baljo/santa_detector/images/HQ/IMG_4454.jpg

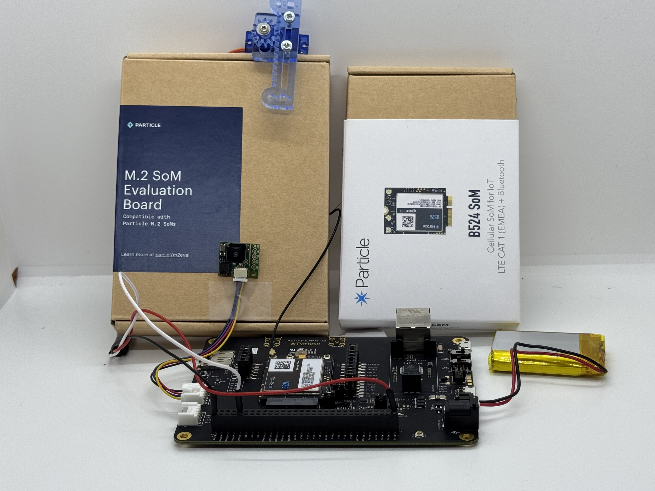
images/HQ/IMG_4454.jpg
