baljo/santa_detector/images/HQ/IMG_4455.jpg

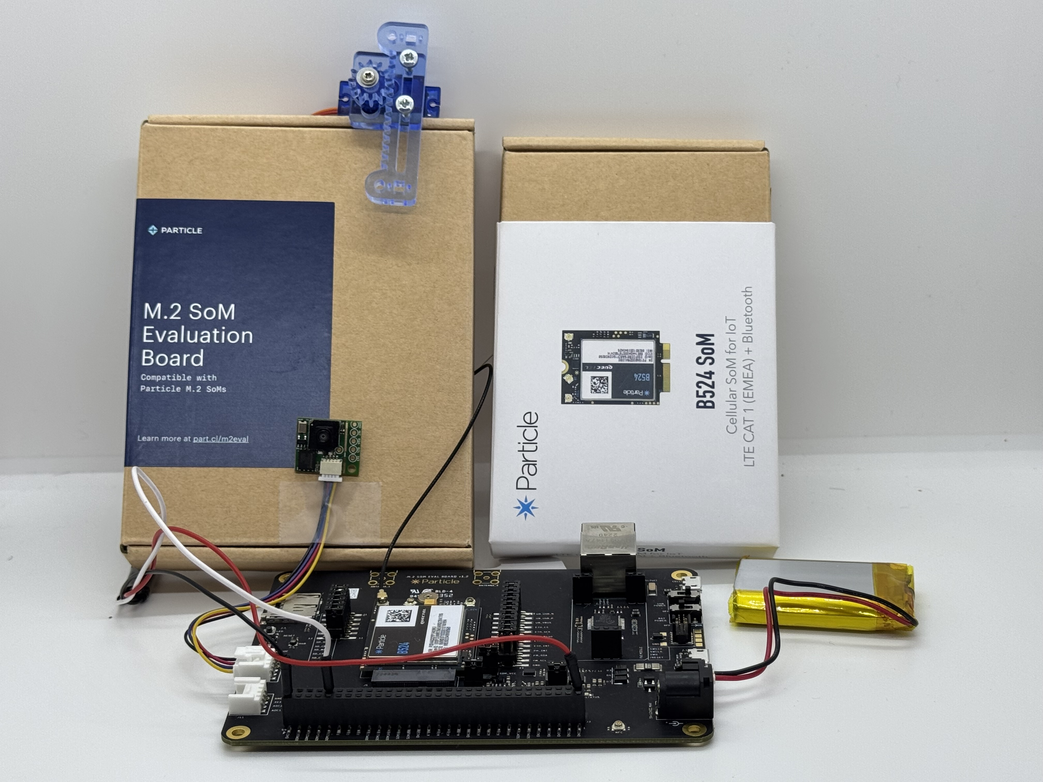
images/HQ/IMG_4455.jpg
