baljo/santa_detector/images/HQ/IMG_4456.jpg

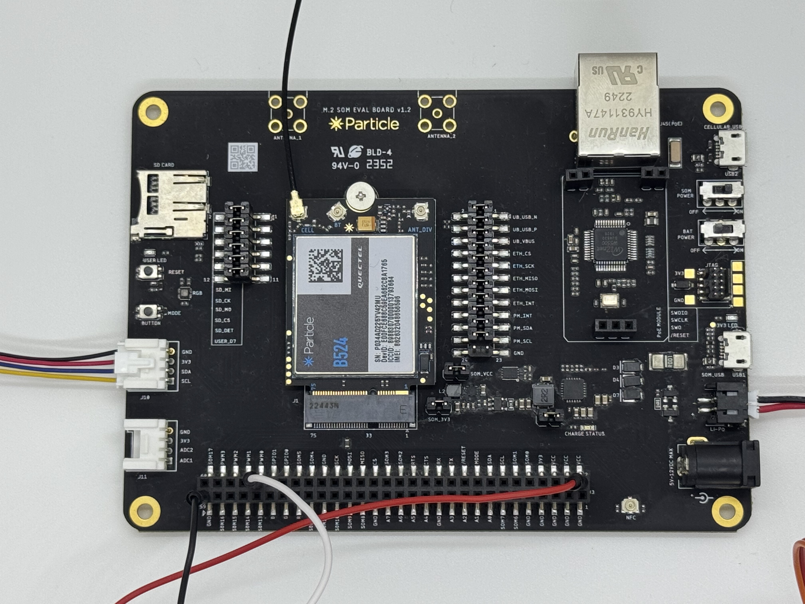
images/HQ/IMG_4456.jpg
