baljo/santa_detector/images/HQ/IMG_4458.jpg

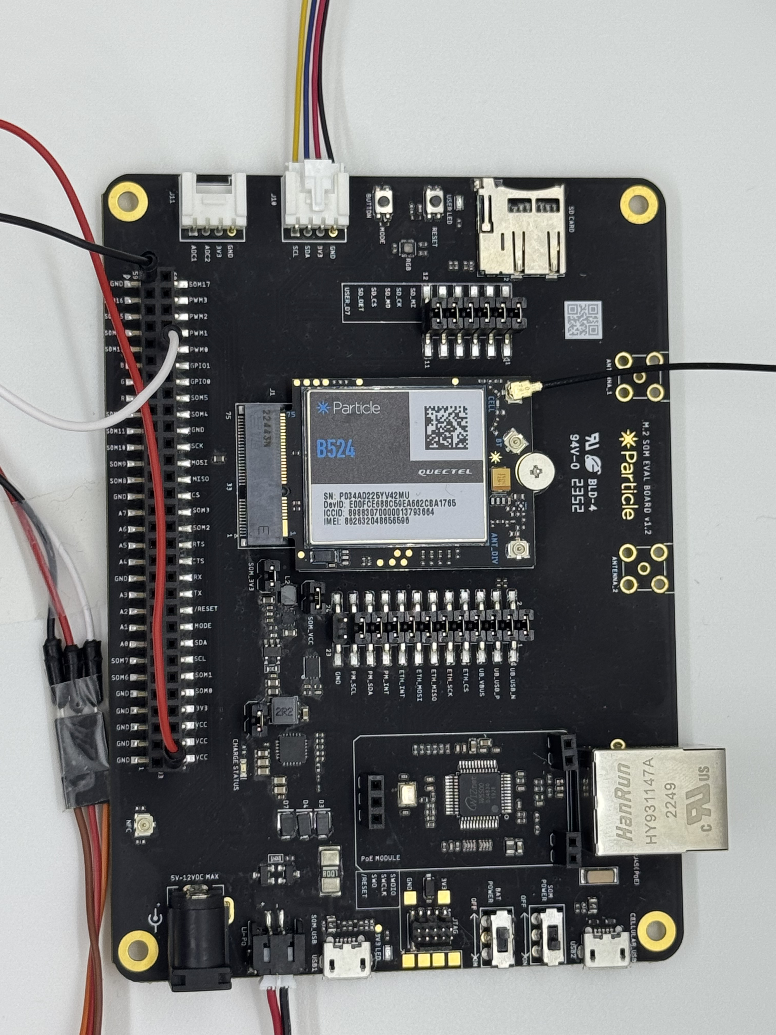
images/HQ/IMG_4458.jpg
