baljo/santa_detector/images/HQ/IMG_4462.jpg

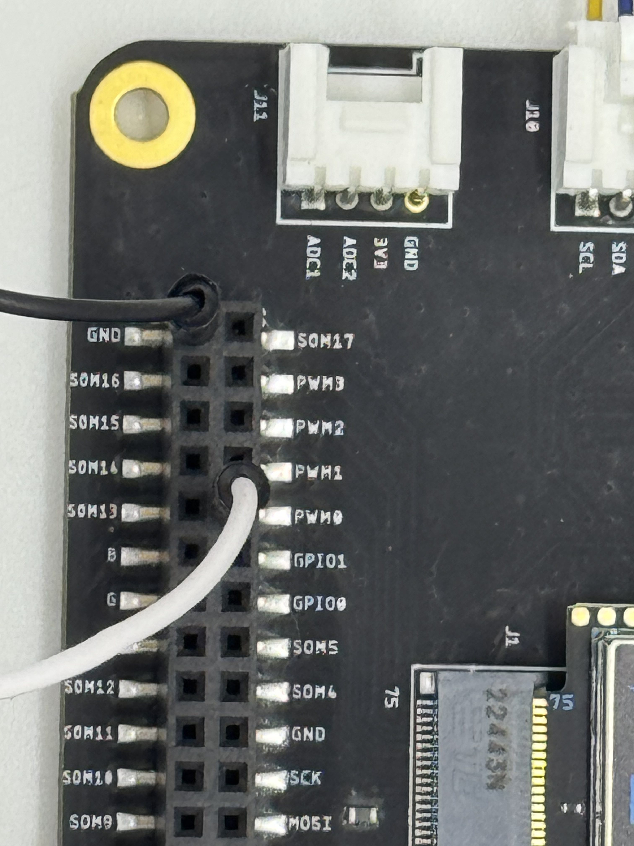
images/HQ/IMG_4462.jpg
