baljo/santa_detector/images/HQ/IMG_4465.jpg

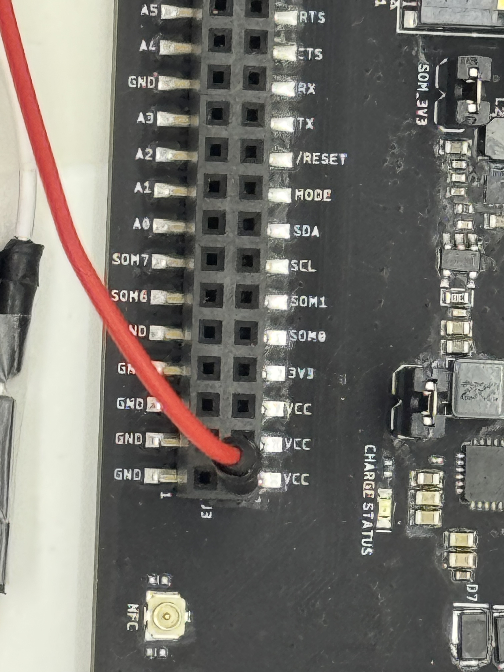
images/HQ/IMG_4465.jpg
