baljo/santa_detector/images/HQ/IMG_4468.jpg

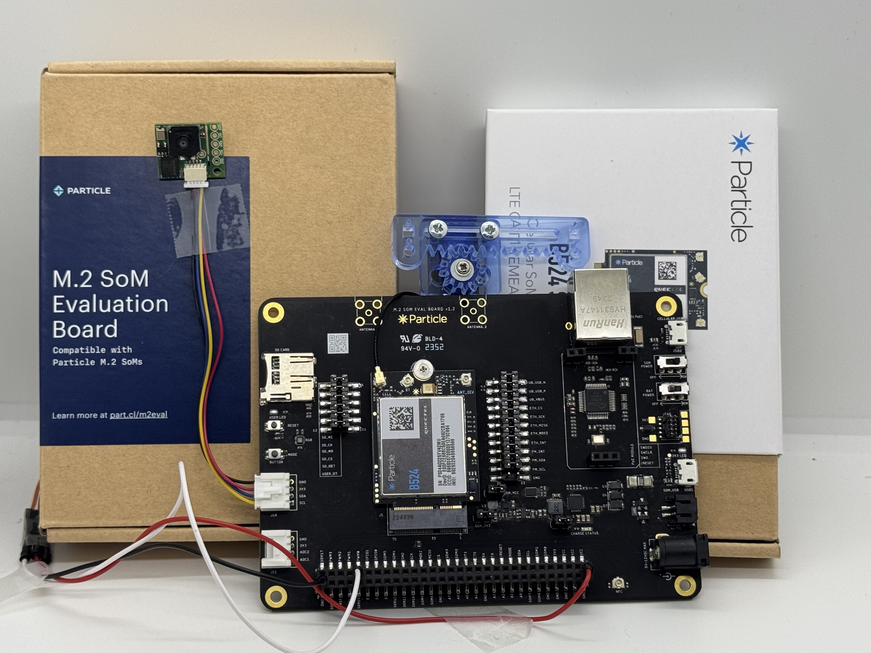
images/HQ/IMG_4468.jpg
