baljo/santa_detector/images/IMG_4441.jpg

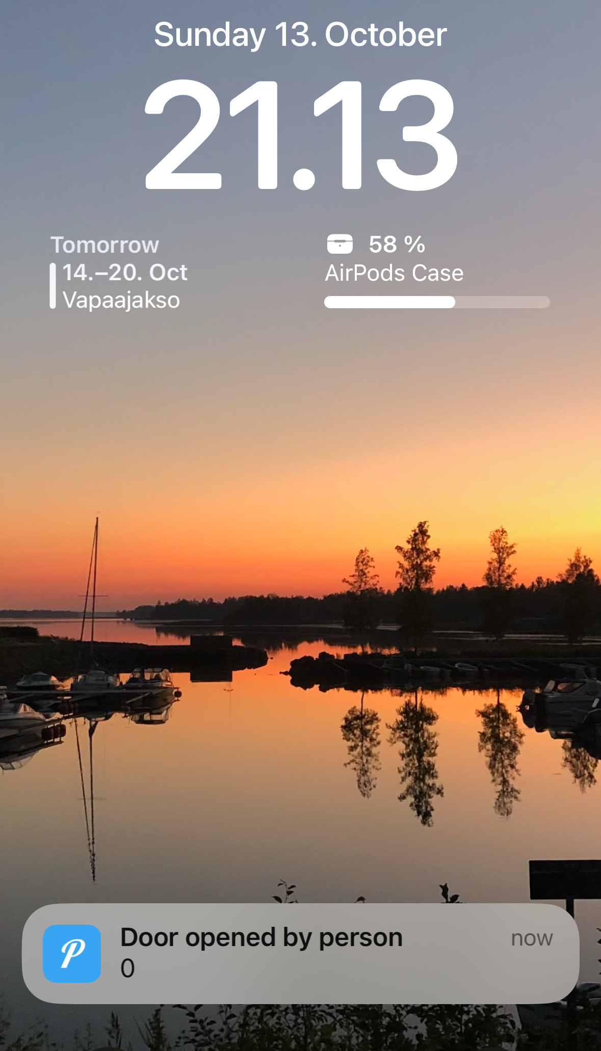
images/IMG_4441.jpg
