baljo/santa_detector/images/IMG_4443.jpg

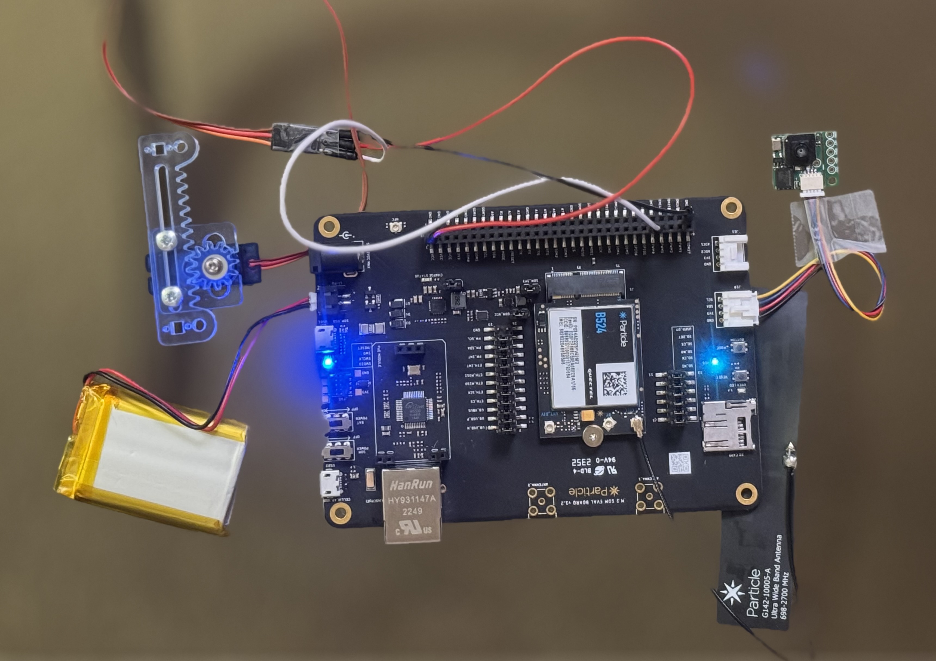
images/IMG_4443.jpg
