baljo/santa_detector/images/IMG_4446.jpg

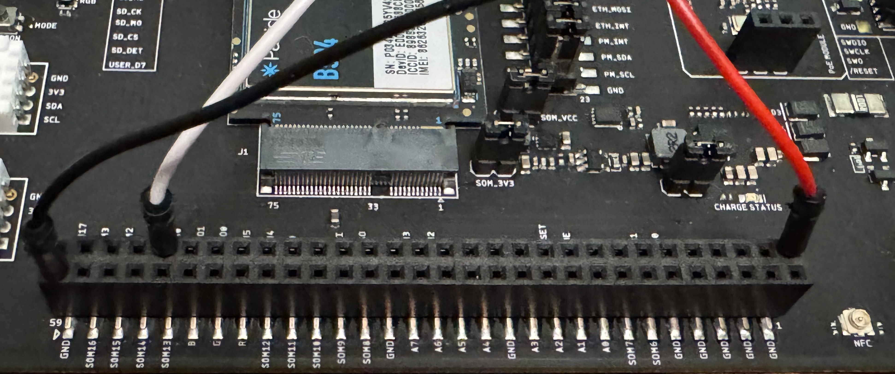
images/IMG_4446.jpg
