baljo/santa_detector/images/IMG_4451.jpg

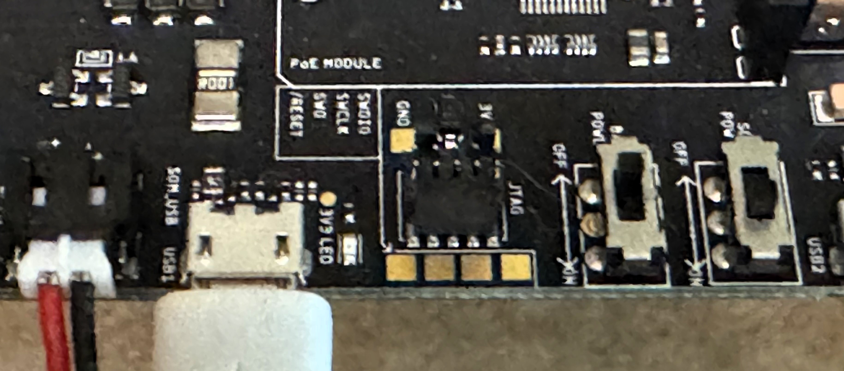
images/IMG_4451.jpg
