baljo/santa_detector/images/IMG_4453.jpg

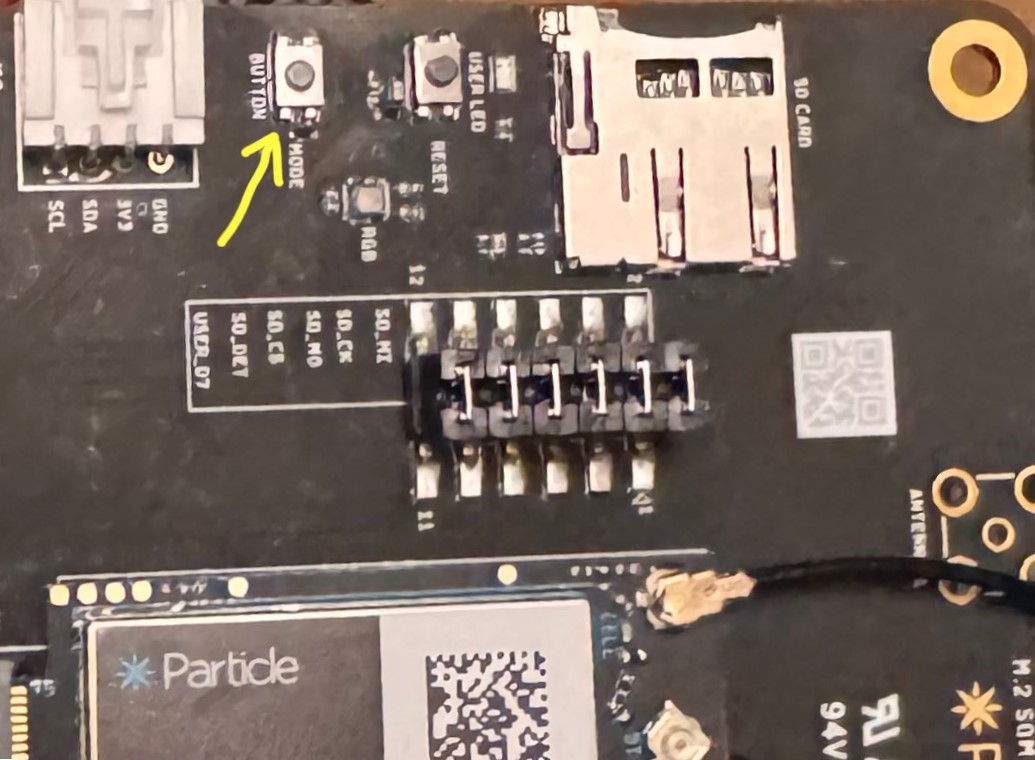
images/IMG_4453.jpg
