baljo/santa_detector/images/IMG_4468_cropped.jpg

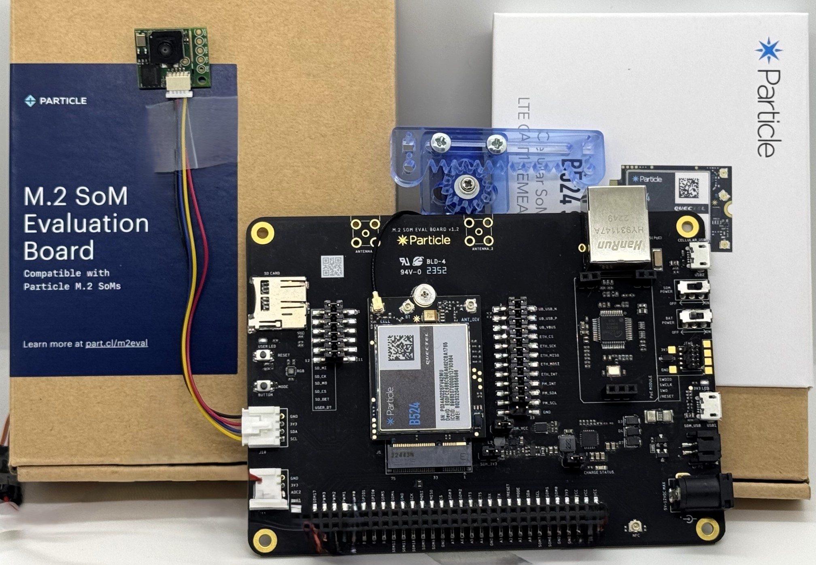
images/IMG_4468_cropped.jpg
