baljo/santa_detector/images/Overview.jpg

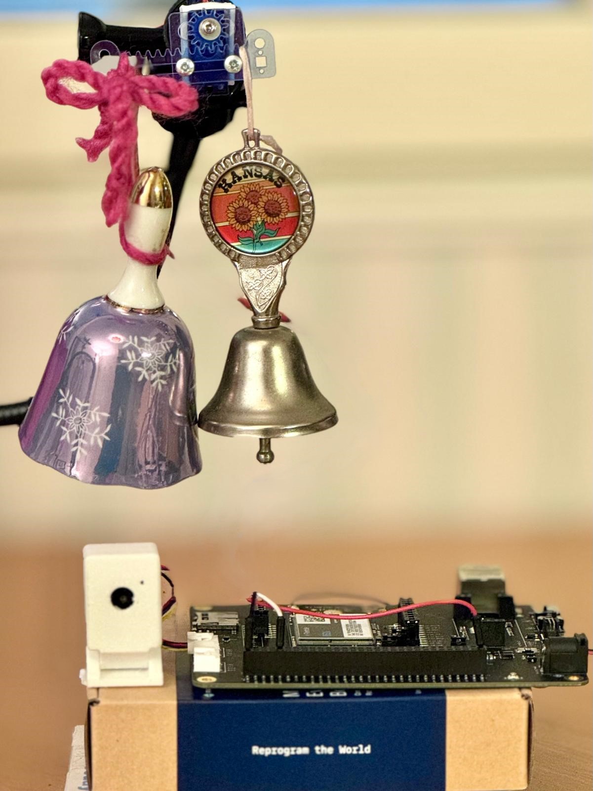
images/Overview.jpg
