baljo/santa_detector/images/Qwiic_Grove_cable.jpg

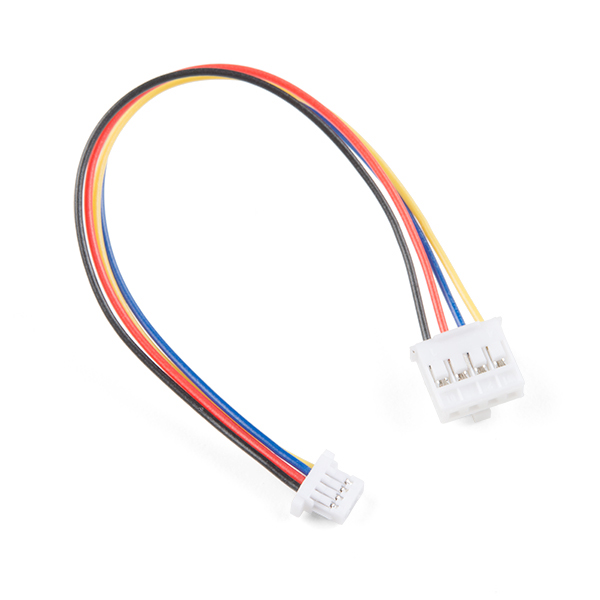
images/Qwiic_Grove_cable.jpg
