baljo/santa_detector/images/Santa_detected.png

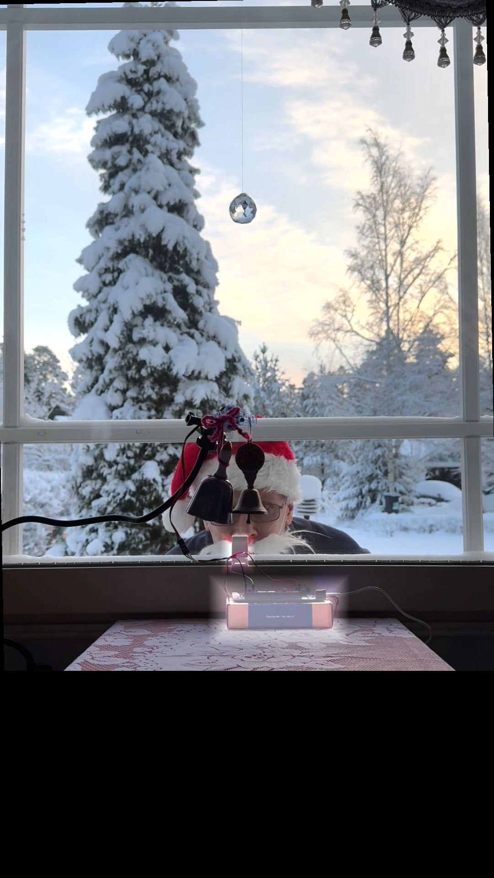
images/Santa_detected.png
