baljo/santa_detector/images/Santa_detected_2.png

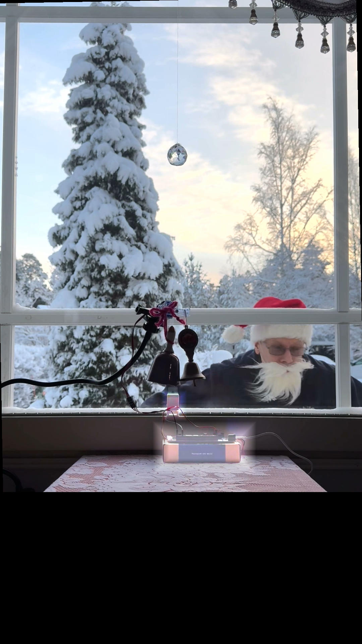
images/Santa_detected_2.png
