baljo/santa_detector/images/Shotcut_00_00_13_001.png

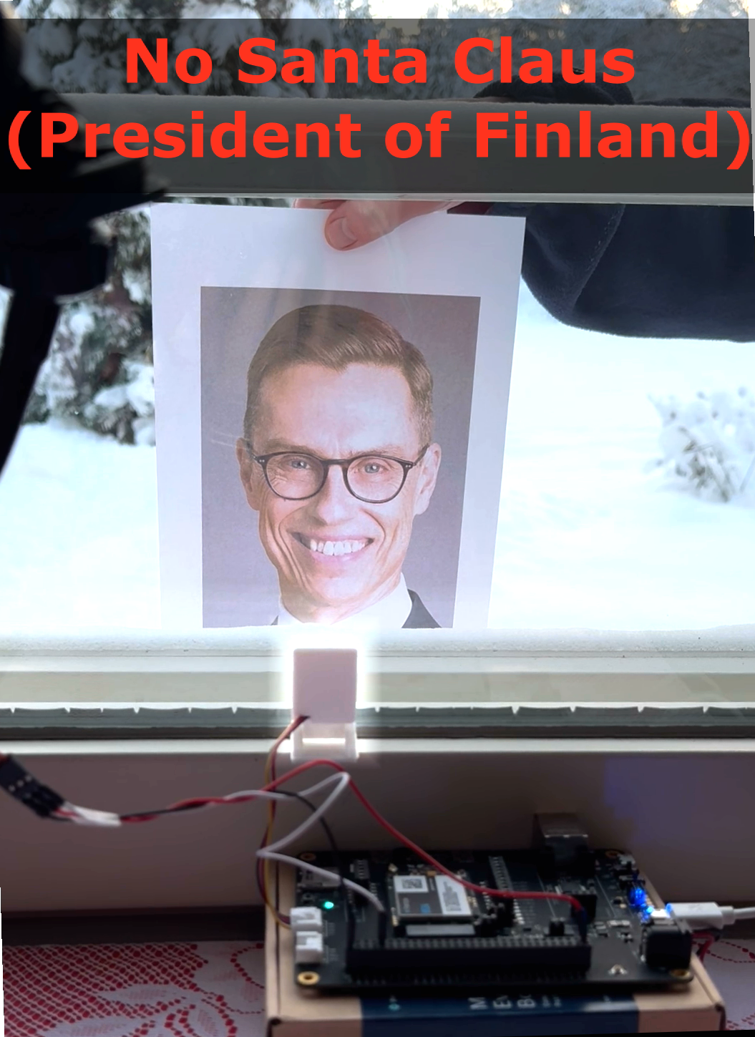
images/Shotcut_00_00_13_001.png
