baljo/santa_detector/images/Shotcut_00_00_41_537.png

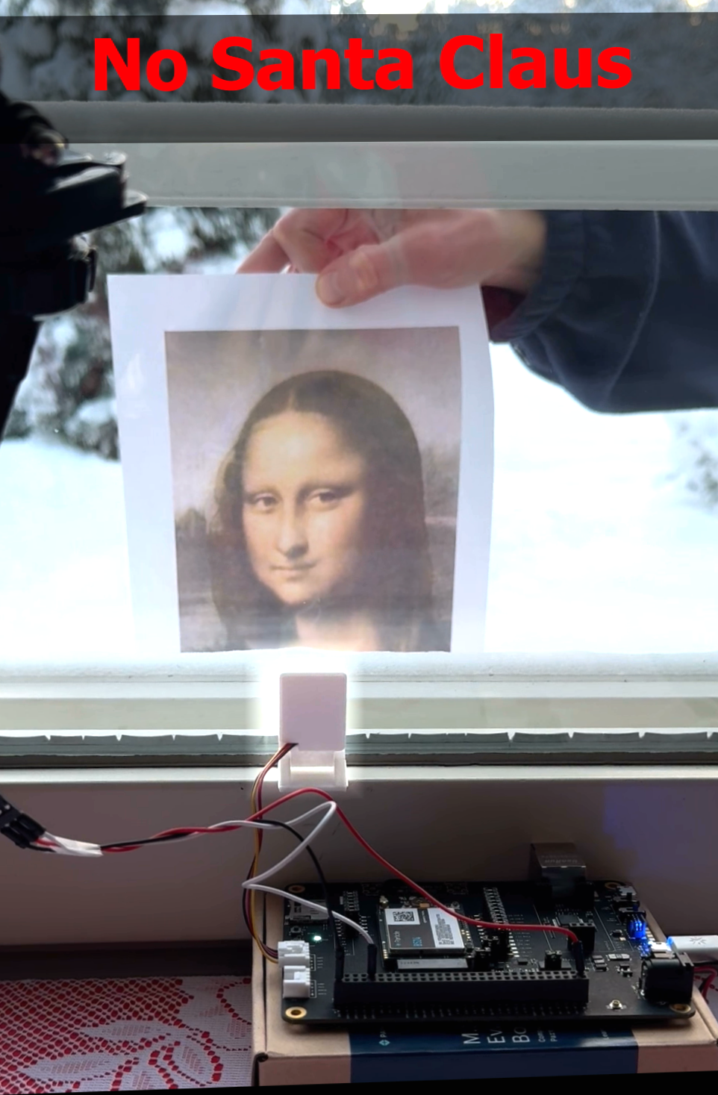
images/Shotcut_00_00_41_537.png
