baljo/santa_detector/video/Jingle Bells.jpg

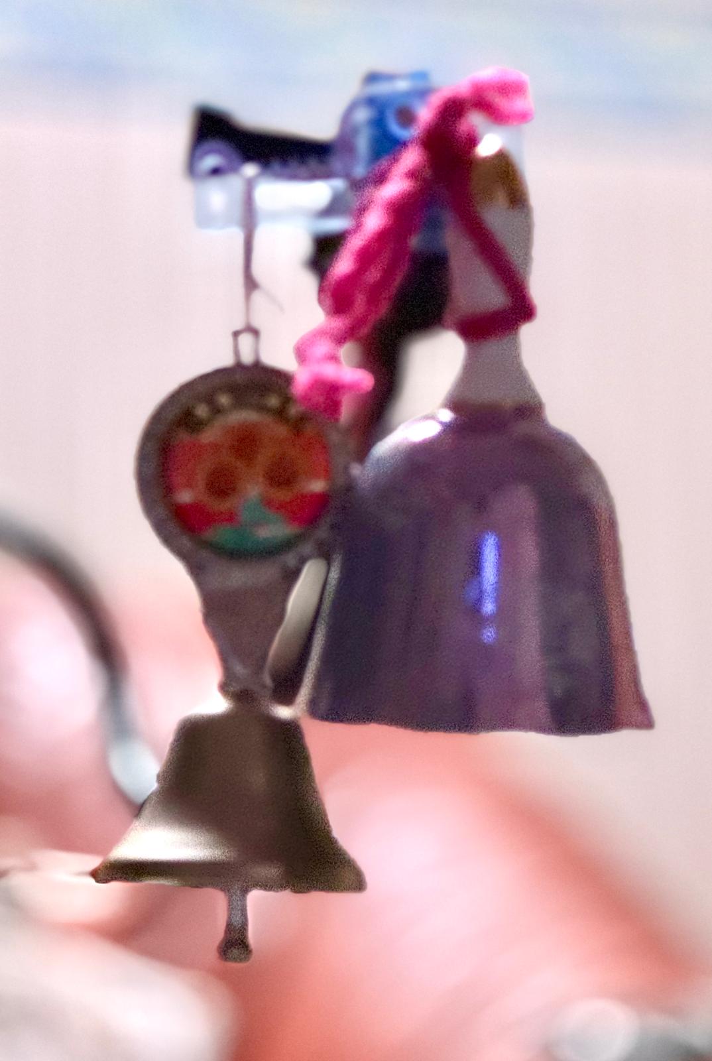
video/Jingle Bells.jpg
