baljo/santa_detector/video/Shotcut_00_00_23_336.png

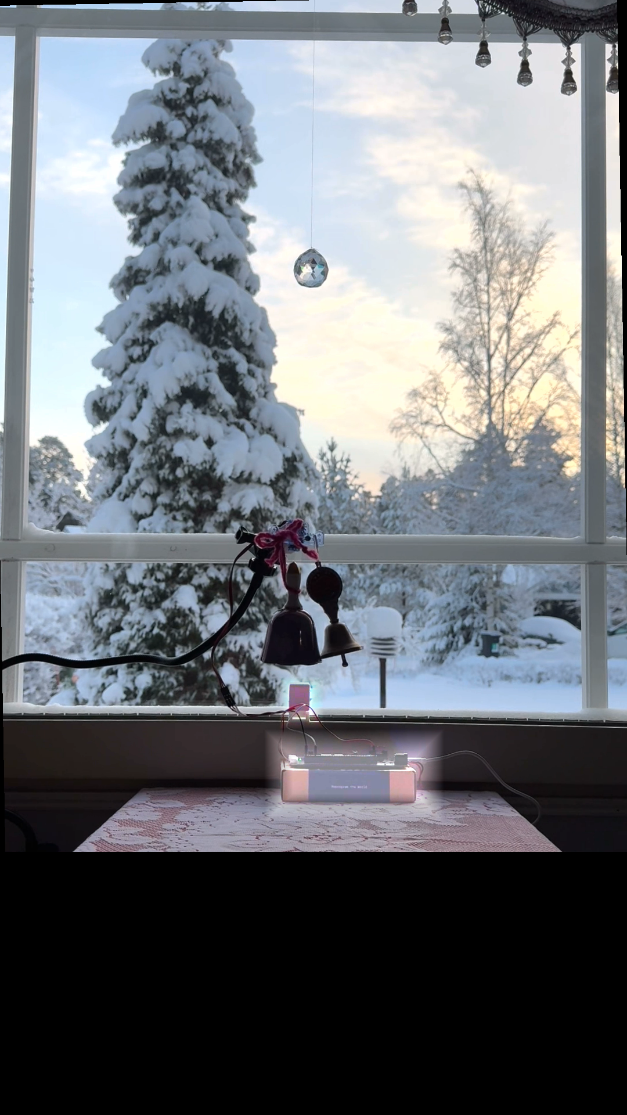
video/Shotcut_00_00_23_336.png
