baljo/santa_detector/images/HQ/IMG_4460.jpg

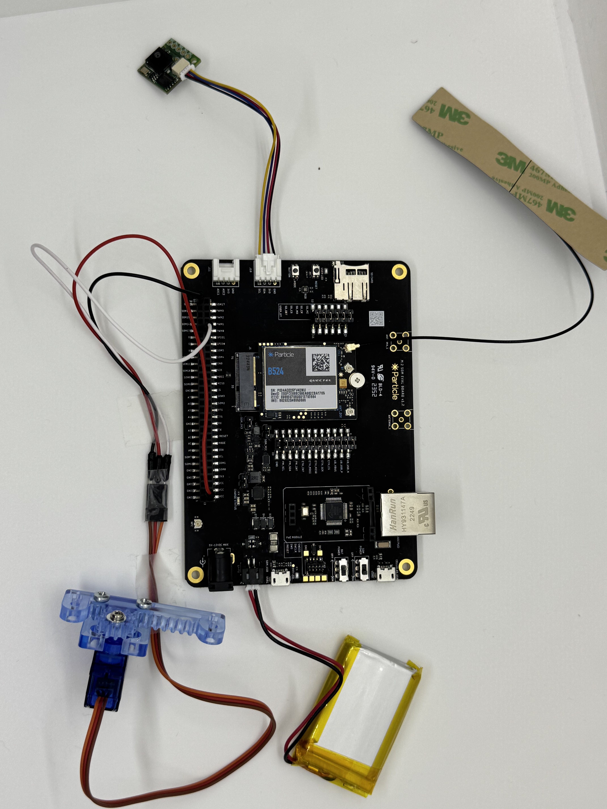
images/HQ/IMG_4460.jpg
